mlab-modules/WINDGAUGE03/doc/img/BOLT_M3x12.png

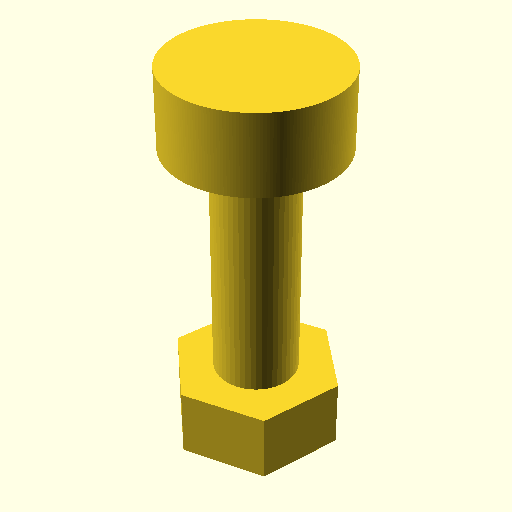
doc/img/BOLT_M3x12.png
