mlab-modules/WINDGAUGE03/doc/img/WINDGAUGE_D02.png

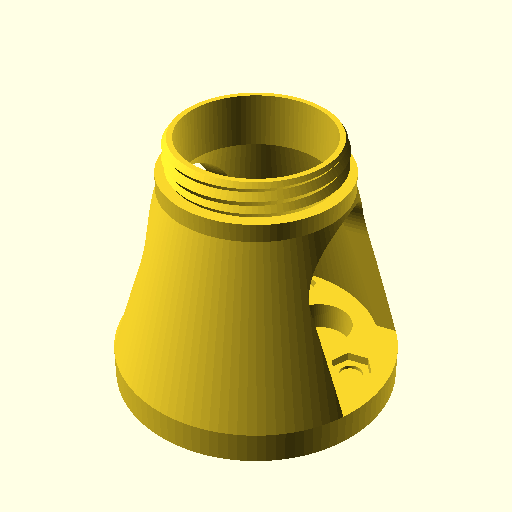
doc/img/WINDGAUGE_D02.png
