mlab-modules/WINDGAUGE03/doc/img/WINDGAUGE_R03.png

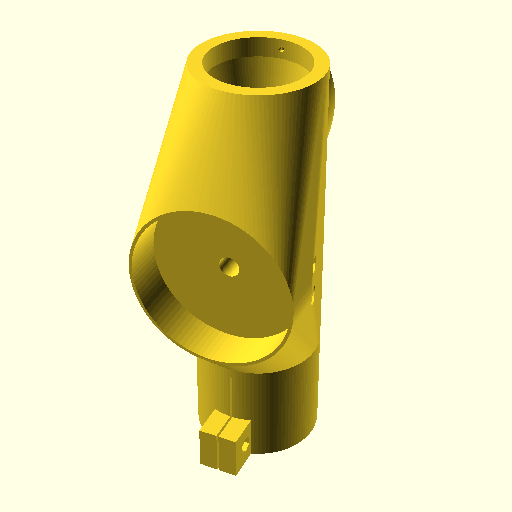
doc/img/WINDGAUGE_R03.png
