mlab-modules/WINDGAUGE03/doc/img/WINDGAUGE_S02.png

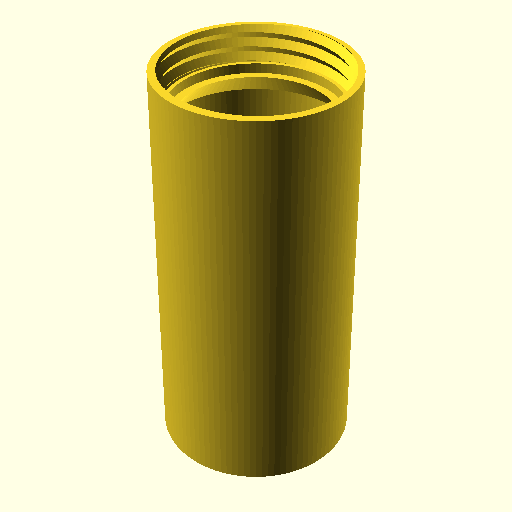
doc/img/WINDGAUGE_S02.png
