mlab-modules/WINDGAUGE03/doc/img/WINDGAUGE_S03.png

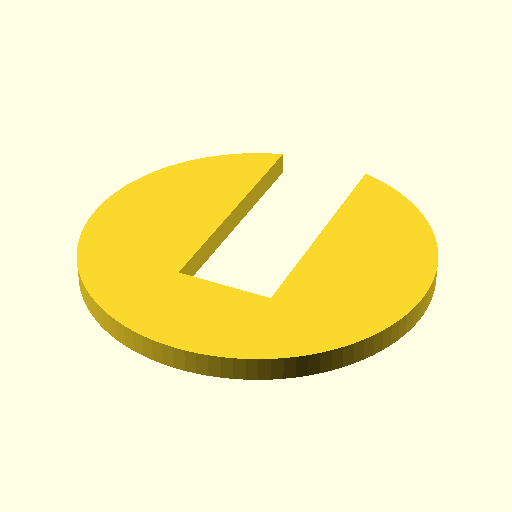
doc/img/WINDGAUGE_S03.png
