mlab-modules/WINDGAUGE03/doc/img/WINDGAUGE_S04.png

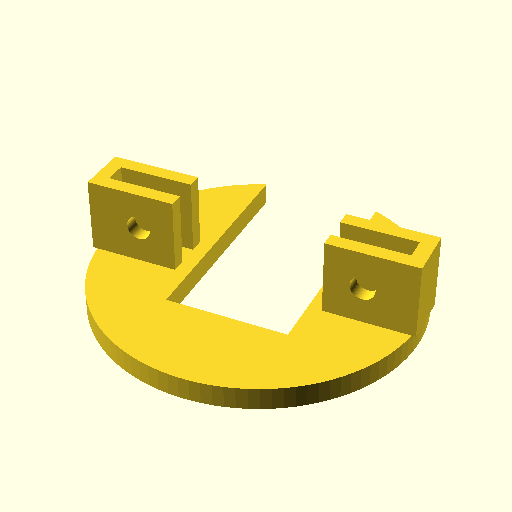
doc/img/WINDGAUGE_S04.png
