mlab-modules/WINDGAUGE03/doc/img/WINDGAUGE_S04_USBI2C01A.png

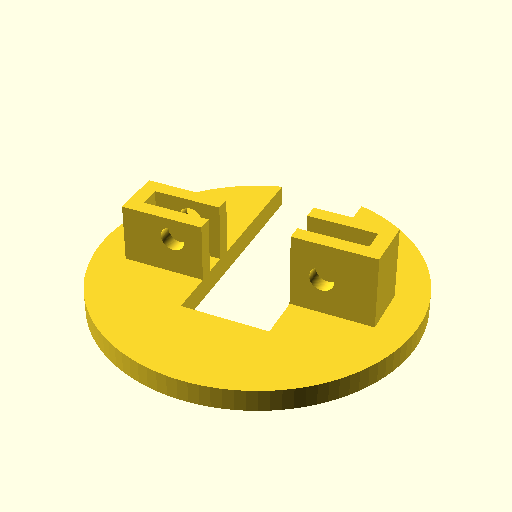
doc/img/WINDGAUGE_S04_USBI2C01A.png
