mlab-modules/WINDGAUGE03/amf/WINDGAUGE_R03.stl

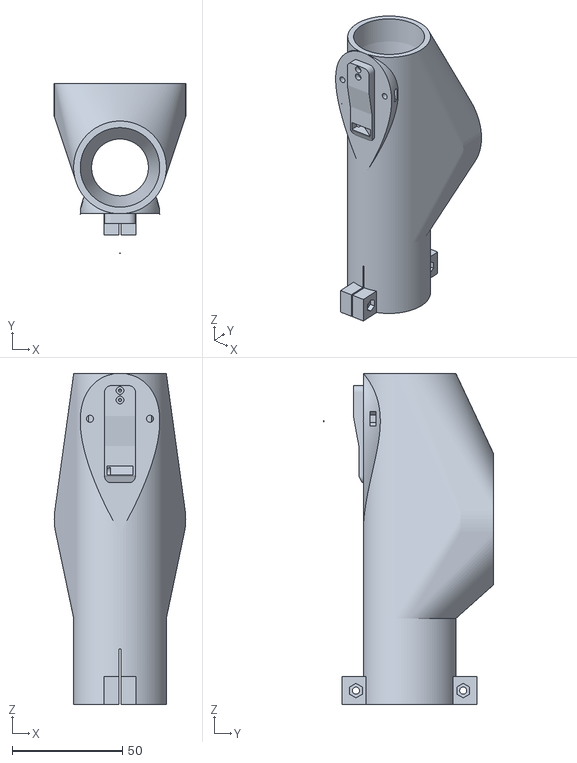
[picture p25: CAD file, 2020-03-23]
amf/WINDGAUGE_R03.stl
59.6 x 77.0 x 150.0
