mlab-modules/WINDGAUGE03/amf/P_WINDGAUGE03A_R03.stl

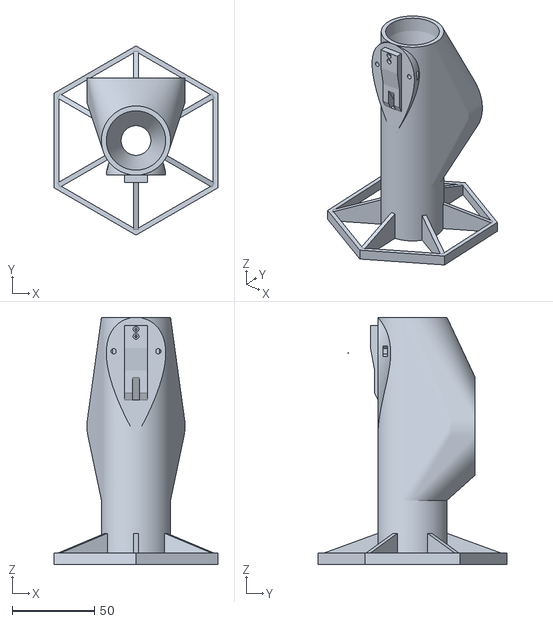
[picture p26: CAD file, 2019-05-01]
amf/P_WINDGAUGE03A_R03.stl
99.5 x 114.9 x 150.0
