mlab-modules/WINDGAUGE03/cad/src/WINDGAUGE_R04.scad

include <../configuration.scad>
include <./lib/polyScrewThread_r1.scad>
use <WINDGAUGE_R03.scad>

//@set_slicing_parameter(perimeters, 6)

draft = true;
$fn = draft ? 20 : 100;

// Drop shape - TOP.
module WINDGAUGE01A_R04(draft = true)
{
    difference()
    {
        drop_shape(2*R03_wide_D, draft);
        translate([-R03_wide_D, -0.001, -3*R03_wide_D])
            cube([2*R03_wide_D, R03_wide_D, 4*R03_wide_D]);
    }
}

difference()
{
    // If not draft -> move to print position.
    if (!draft)
        translate([0, R03_wide_D/2, 0])
            rotate([270, 0, 90])
                WINDGAUGE01A_R04(false);
    else
        WINDGAUGE01A_R04();
    // Cut-out cube not needed in this model
    //if (draft)
    //    translate([0, -R03_wide_D, -2*R03_wide_D])
    //        cube(10);
}
